MOUmeiqi/PhD-Resources/Misc. Images/2-r2.jpg

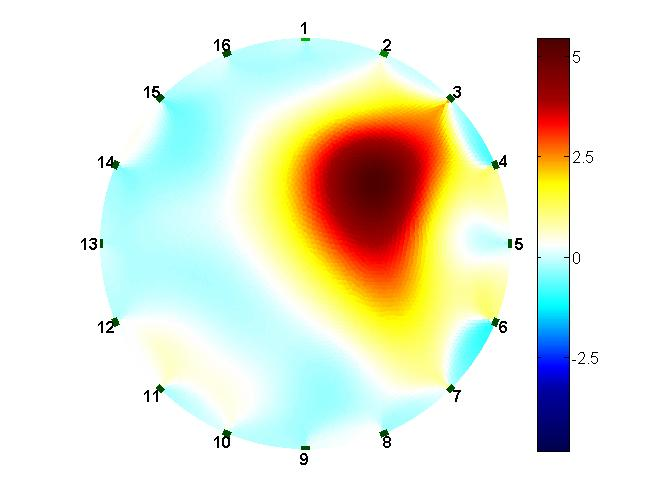
Misc. Images/2-r2.jpg
