MOUmeiqi/PhD-Resources/Misc. Images/3-r3a.jpg

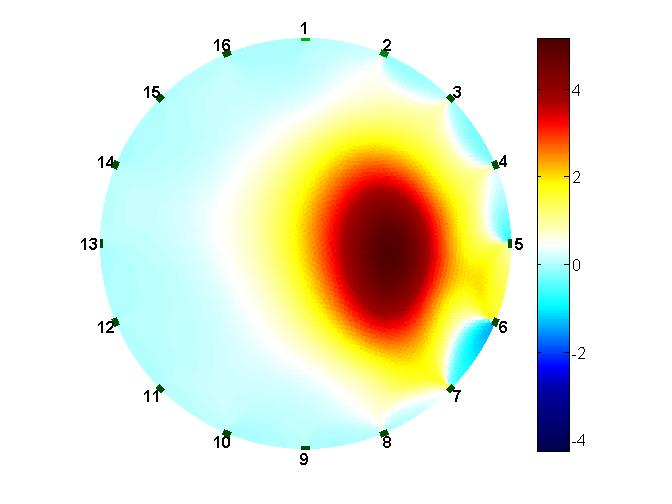
Misc. Images/3-r3a.jpg
