MOUmeiqi/PhD-Resources/Misc. Images/4-r4an.jpg

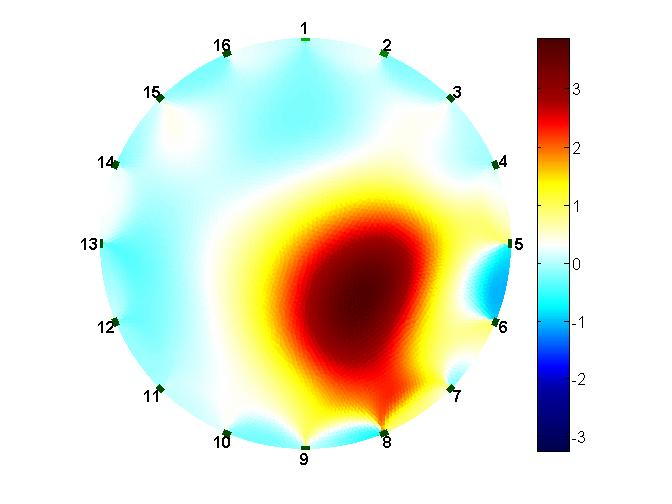
Misc. Images/4-r4an.jpg
