MOUmeiqi/PhD-Resources/Misc. Images/5-r5a.jpg

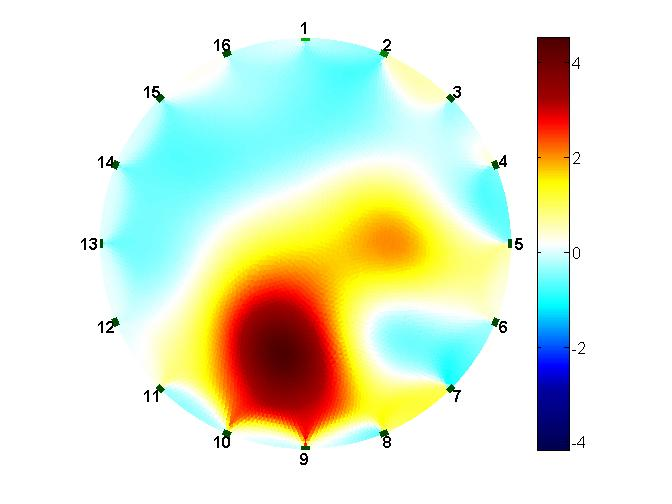
Misc. Images/5-r5a.jpg
