MOUmeiqi/PhD-Resources/Misc. Images/7-r7a.jpg

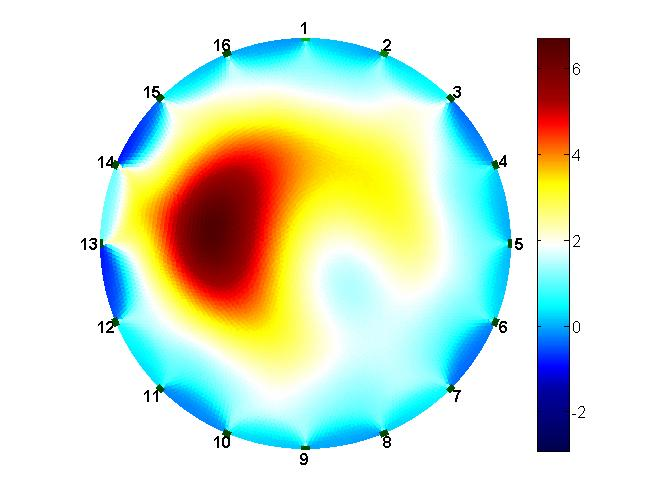
Misc. Images/7-r7a.jpg
