MOUmeiqi/PhD-Resources/Misc. Images/14-r103.jpg

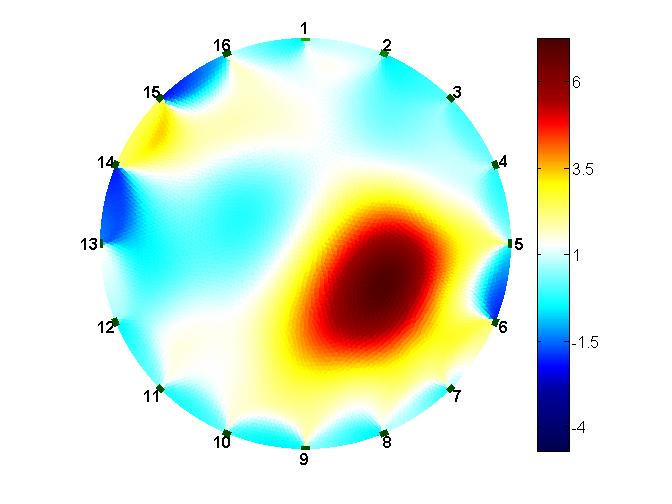
Misc. Images/14-r103.jpg
