MOUmeiqi/PhD-Resources/Misc. Images/n4aANDh4.jpg

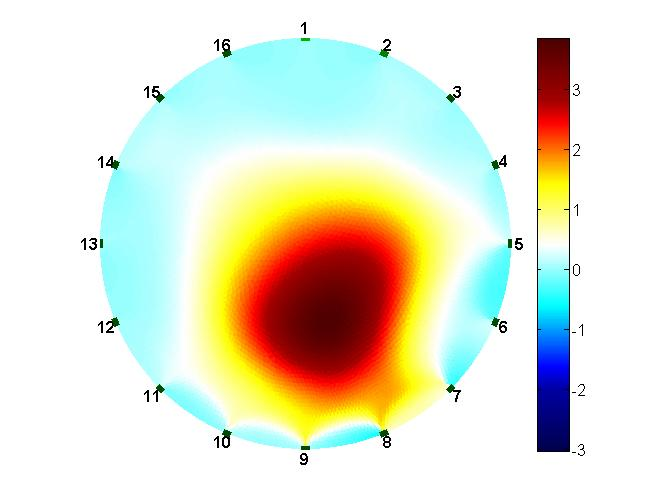
Misc. Images/n4aANDh4.jpg
