MOUmeiqi/PhD-Resources/Misc. Images/r1n.jpg

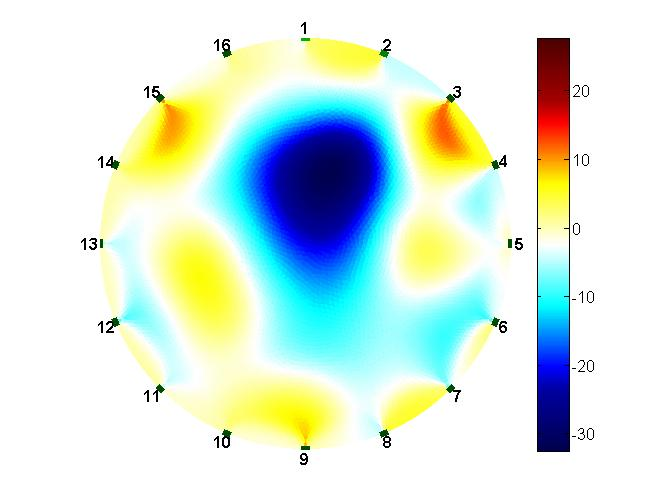
Misc. Images/r1n.jpg
