MOUmeiqi/PhD-Resources/Misc. Images/r2n.jpg

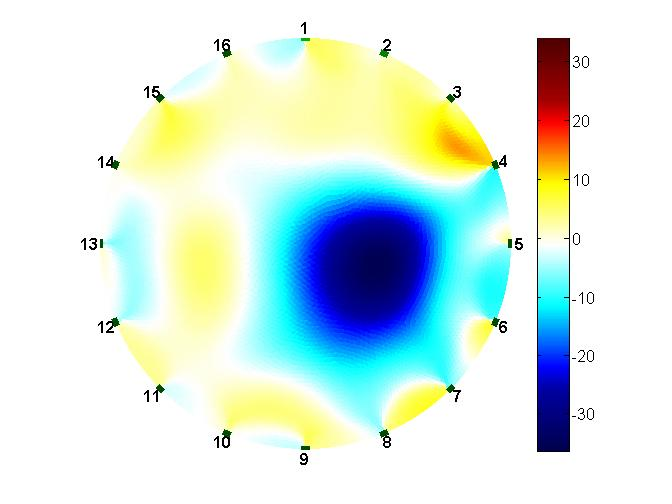
Misc. Images/r2n.jpg
