MOUmeiqi/PhD-Resources/Misc. Images/r3n.jpg

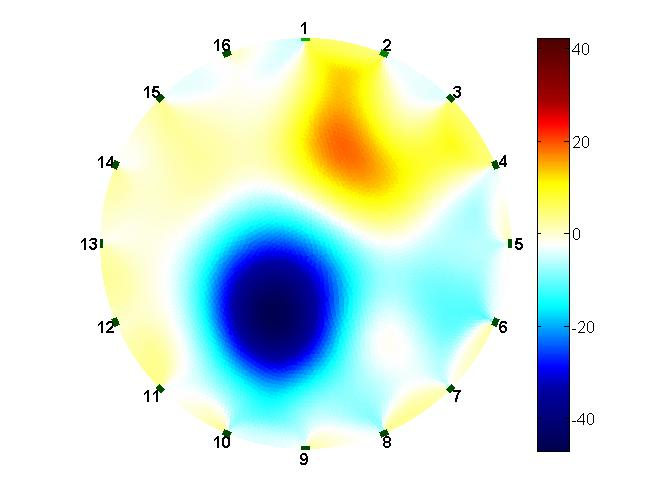
Misc. Images/r3n.jpg
