MOUmeiqi/PhD-Resources/Misc. Images/r6n.jpg

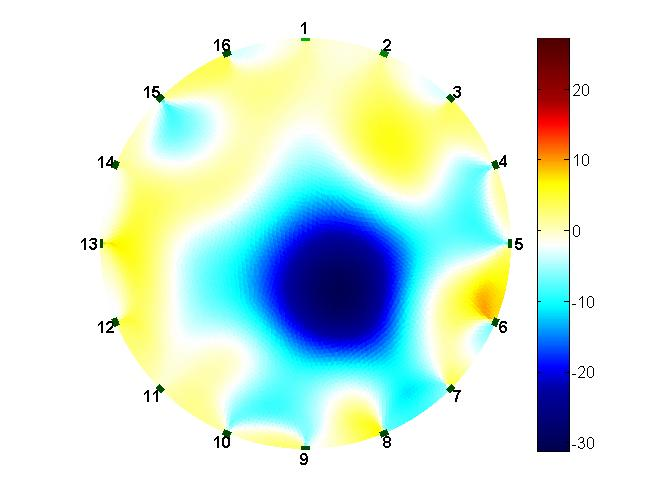
Misc. Images/r6n.jpg
