MOUmeiqi/PhD-Resources/Misc. Images/r7n.jpg

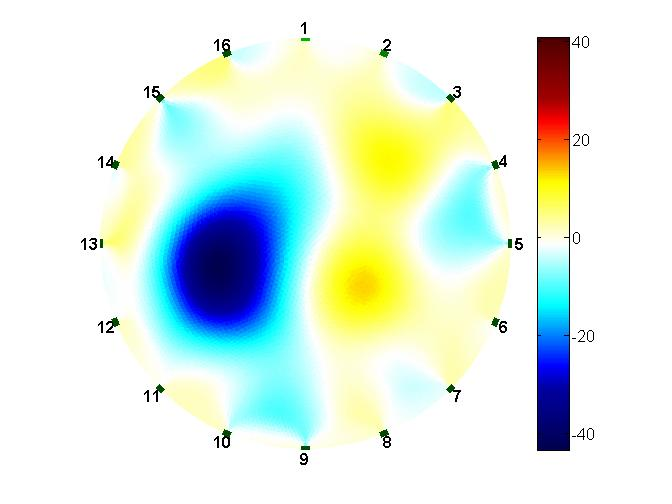
Misc. Images/r7n.jpg
