MOUmeiqi/PhD-Resources/Misc. Images/r8n.jpg

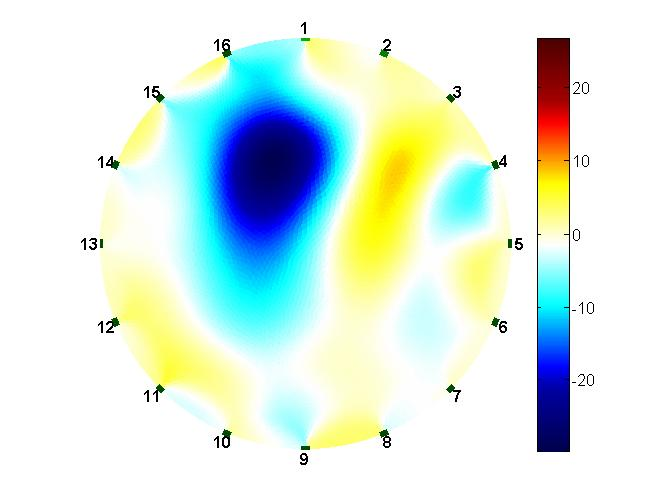
Misc. Images/r8n.jpg
