MOUmeiqi/PhD-Resources/Misc. Images/r11n.jpg

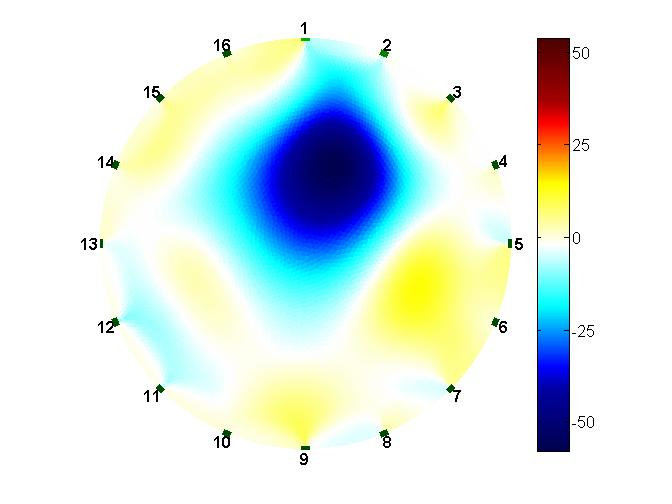
Misc. Images/r11n.jpg
