MOUmeiqi/PhD-Resources/Misc. Images/r21n.jpg

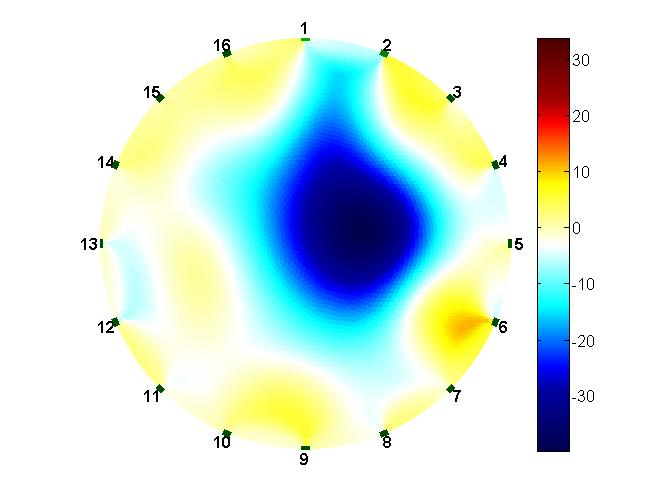
Misc. Images/r21n.jpg
