MOUmeiqi/PhD-Resources/Misc. Images/r31n.jpg

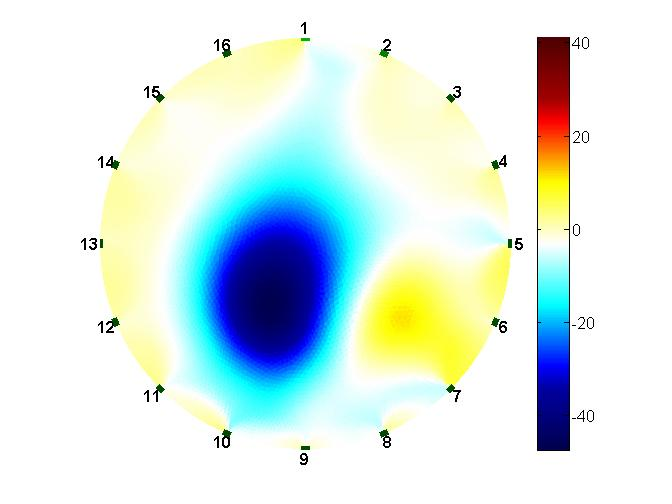
Misc. Images/r31n.jpg
