MOUmeiqi/PhD-Resources/Misc. Images/r41n.jpg

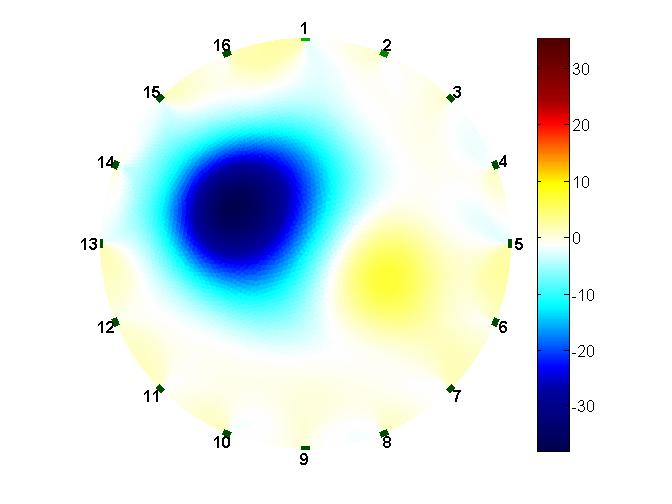
Misc. Images/r41n.jpg
