MOUmeiqi/PhD-Resources/Misc. Images/r_n2a_h2a.jpg

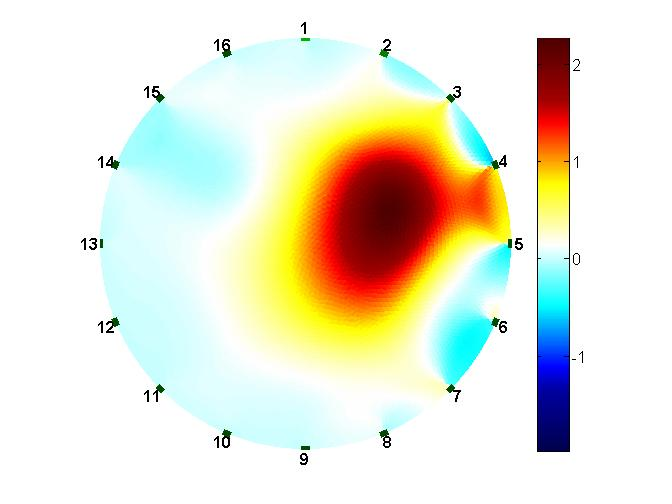
Misc. Images/r_n2a_h2a.jpg
