MOUmeiqi/PhD-Resources/Misc. Images/r_n3a_h3a.jpg

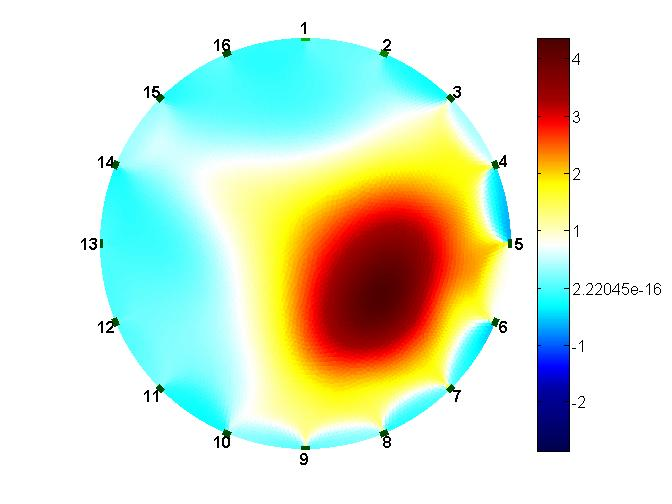
Misc. Images/r_n3a_h3a.jpg
