MOUmeiqi/PhD-Resources/Misc. Images/r_n3a_h3a_2.jpg

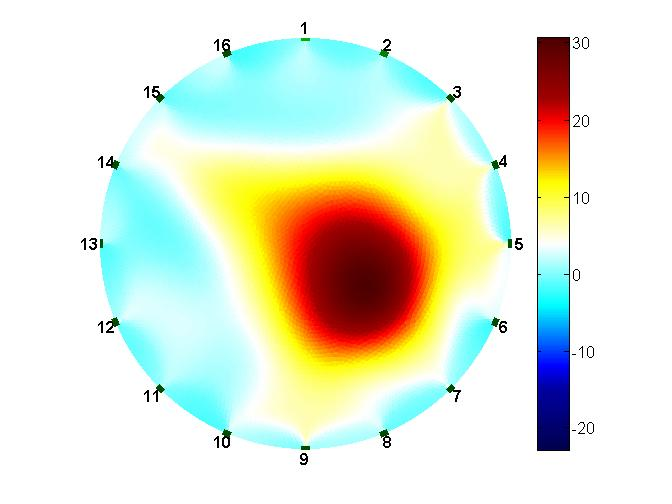
Misc. Images/r_n3a_h3a_2.jpg
