MOUmeiqi/PhD-Resources/Misc. Images/r_n4a_h4.jpg

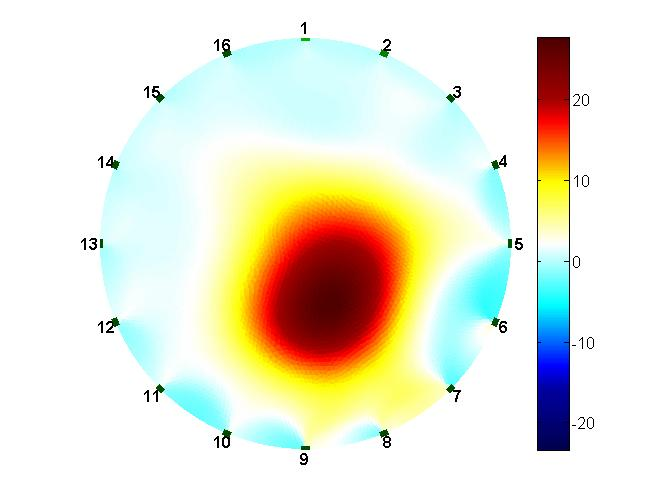
Misc. Images/r_n4a_h4.jpg
