MOUmeiqi/PhD-Resources/Misc. Images/r_n5a_h5_2.jpg

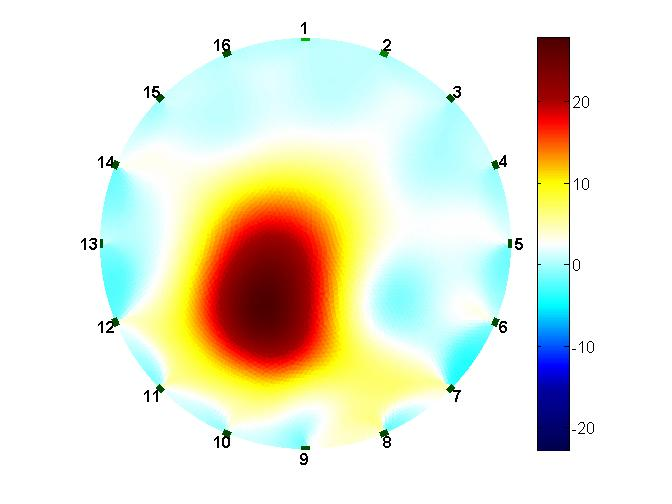
Misc. Images/r_n5a_h5_2.jpg
