MOUmeiqi/PhD-Resources/Misc. Images/r_n6a_h6.jpg

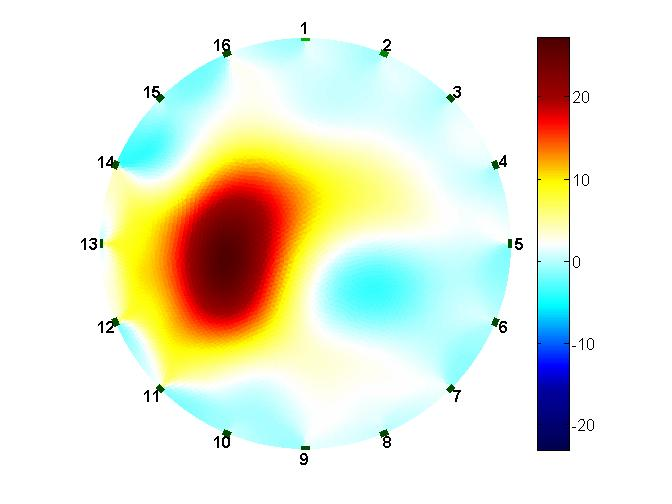
Misc. Images/r_n6a_h6.jpg
