MOUmeiqi/PhD-Resources/Misc. Images/r_n7a_h7.jpg

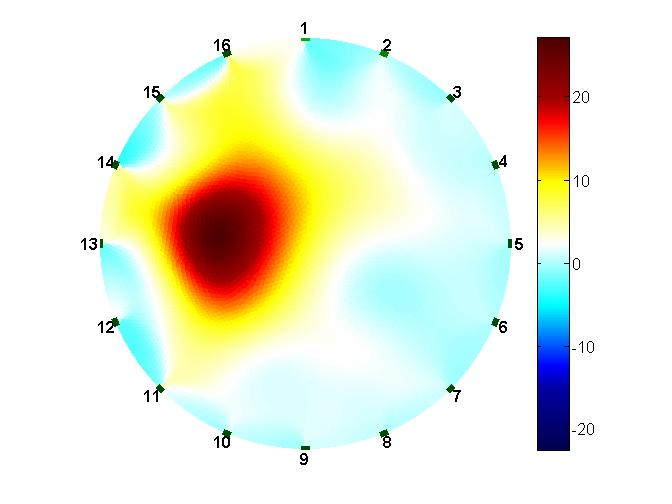
Misc. Images/r_n7a_h7.jpg
