MOUmeiqi/PhD-Resources/Misc. Images/rd1.jpg

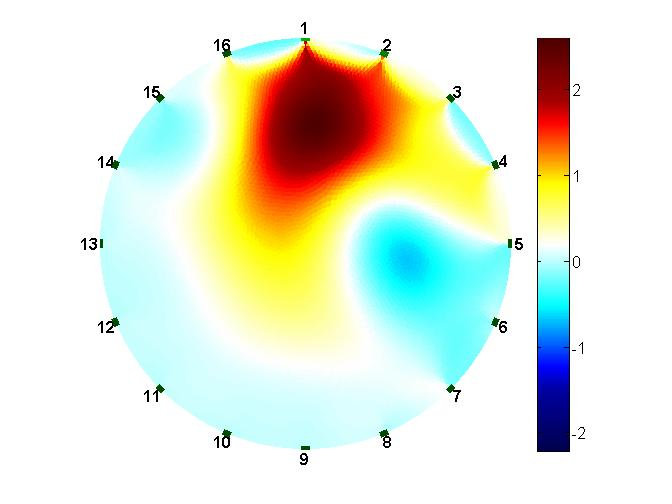
Misc. Images/rd1.jpg
