MOUmeiqi/PhD-Resources/Misc. Images/rd2.jpg

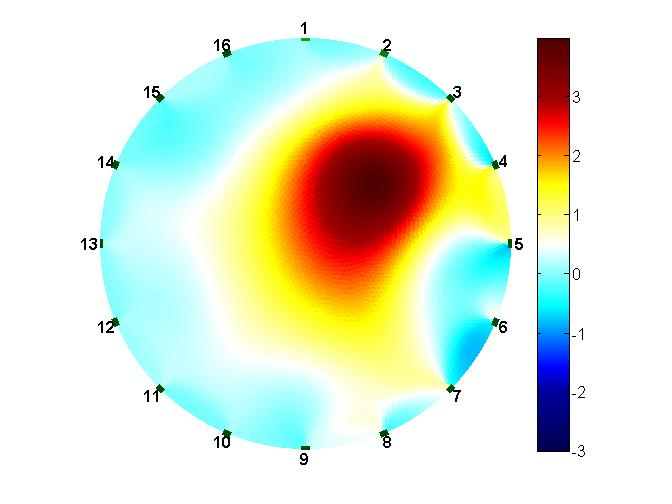
Misc. Images/rd2.jpg
