MOUmeiqi/PhD-Resources/Misc. Images/rd3.jpg

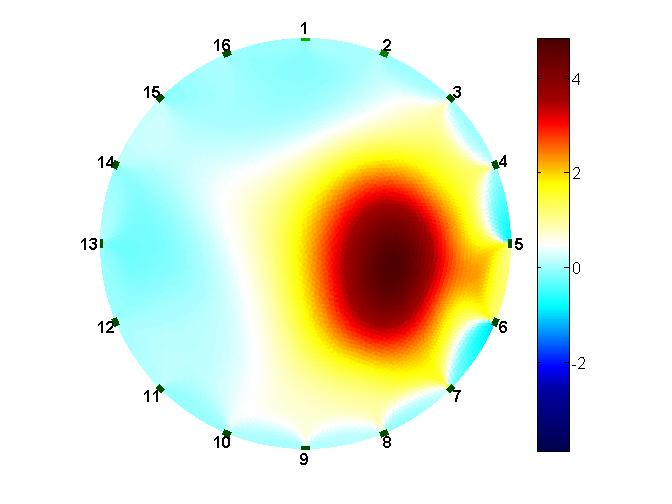
Misc. Images/rd3.jpg
