MOUmeiqi/PhD-Resources/Misc. Images/rd4.jpg

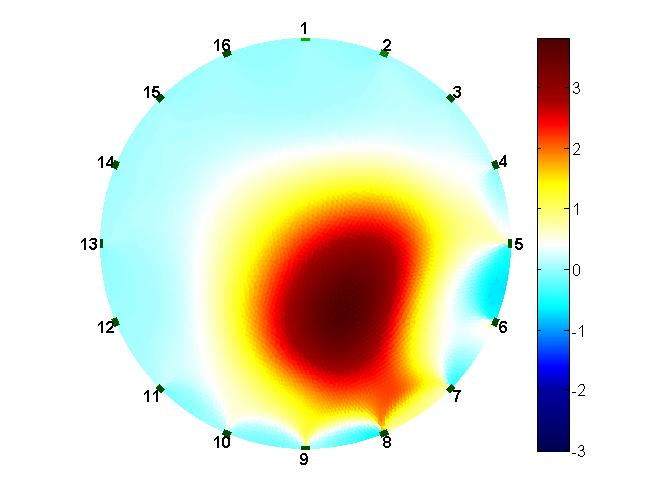
Misc. Images/rd4.jpg
