MOUmeiqi/PhD-Resources/Misc. Images/rd4n.jpg

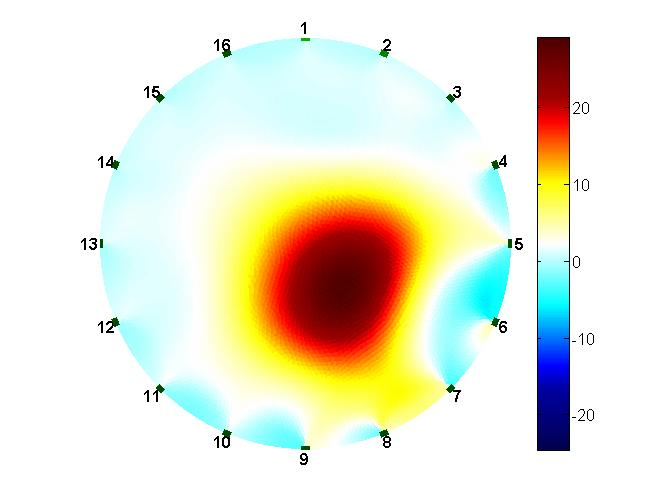
Misc. Images/rd4n.jpg
