MOUmeiqi/PhD-Resources/Misc. Images/rd5.jpg

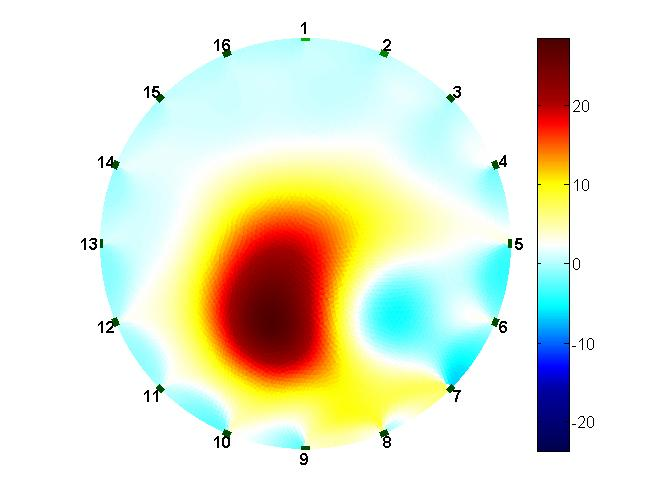
Misc. Images/rd5.jpg
