MOUmeiqi/PhD-Resources/Misc. Images/rd9.jpg

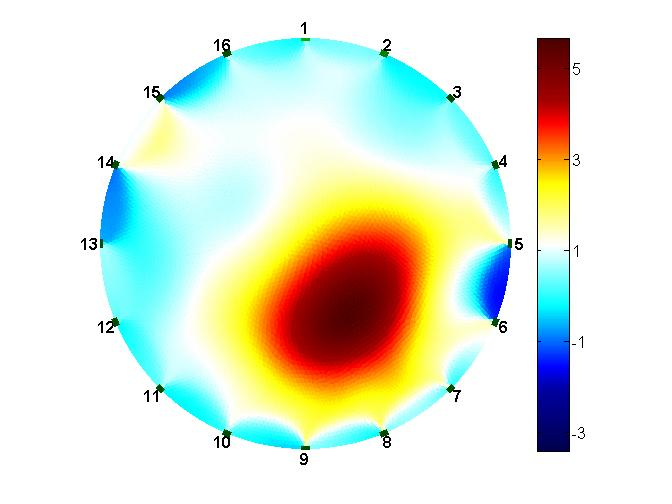
Misc. Images/rd9.jpg
