MOUmeiqi/PhD-Resources/Misc. Images/rdf1n.jpg

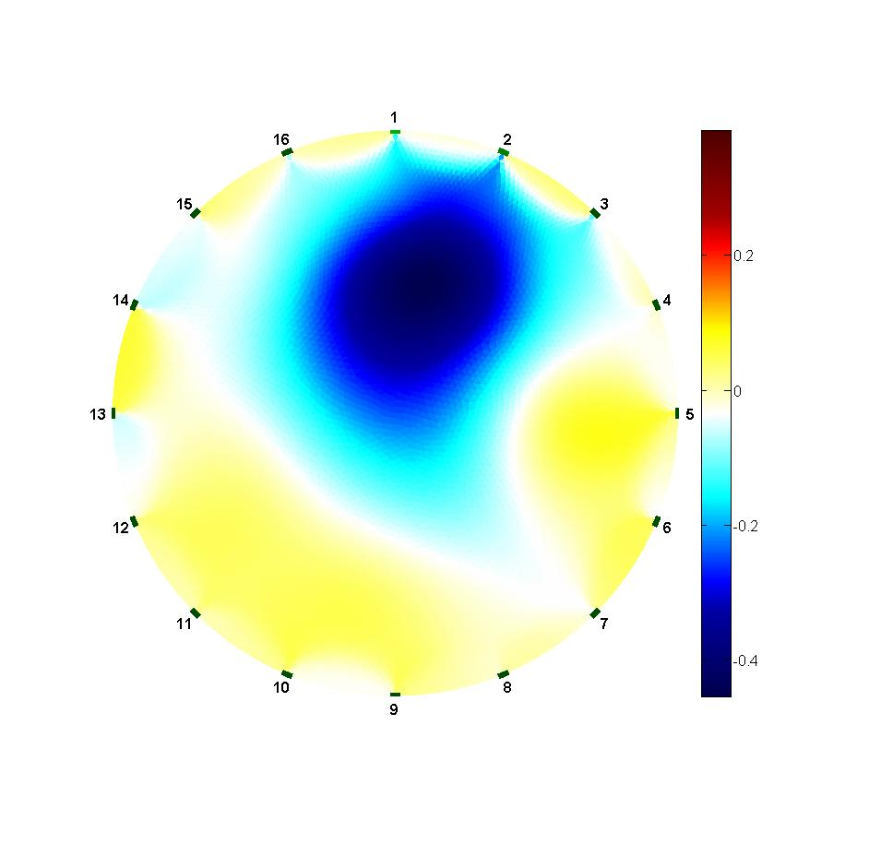
Misc. Images/rdf1n.jpg
