MOUmeiqi/PhD-Resources/Misc. Images/rdf2.jpg

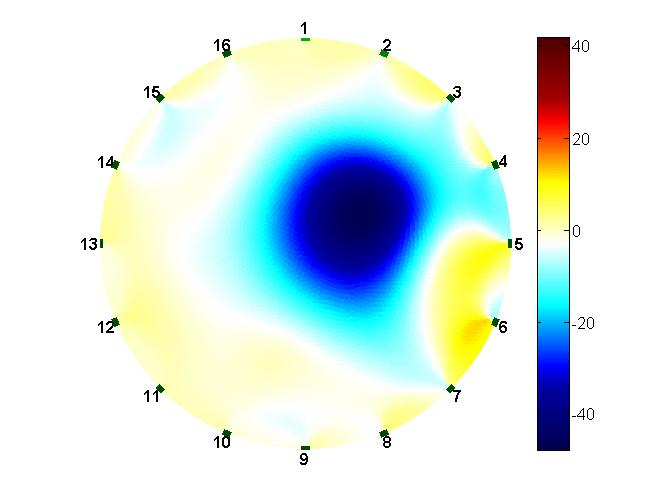
Misc. Images/rdf2.jpg
