MOUmeiqi/PhD-Resources/Misc. Images/rdf3.jpg

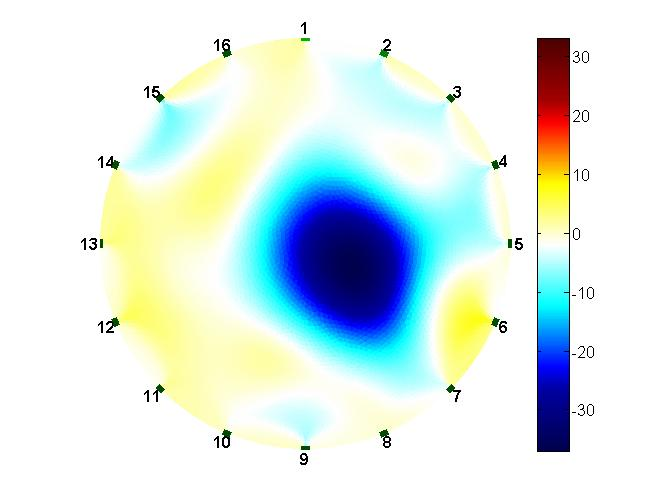
Misc. Images/rdf3.jpg
