MOUmeiqi/PhD-Resources/Misc. Images/rdf4.jpg

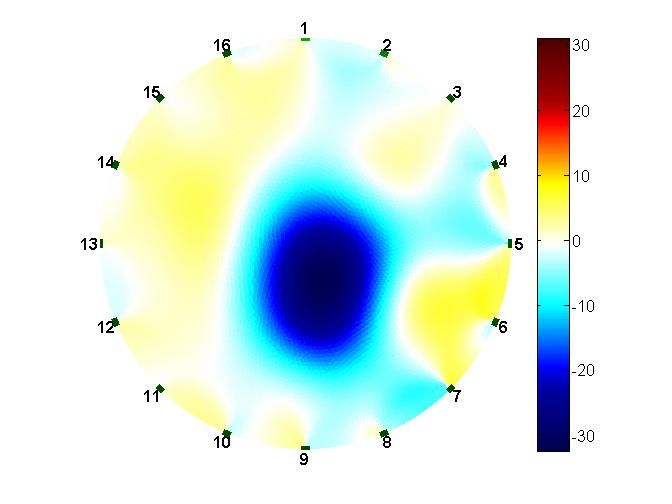
Misc. Images/rdf4.jpg
