MOUmeiqi/PhD-Resources/Misc. Images/rdf5.jpg

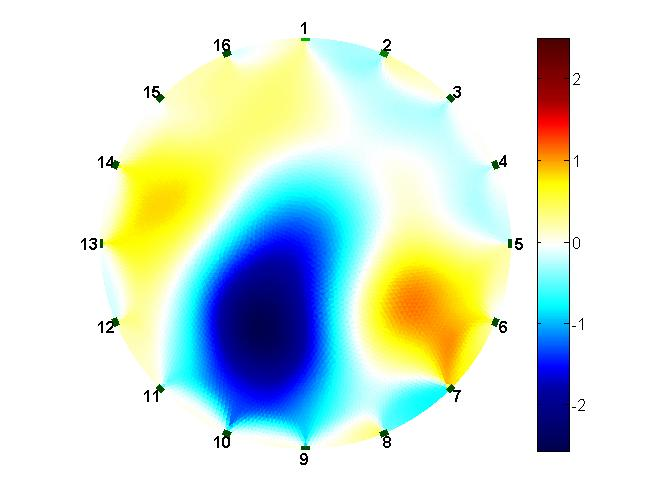
Misc. Images/rdf5.jpg
