MOUmeiqi/PhD-Resources/Misc. Images/rdf5n.jpg

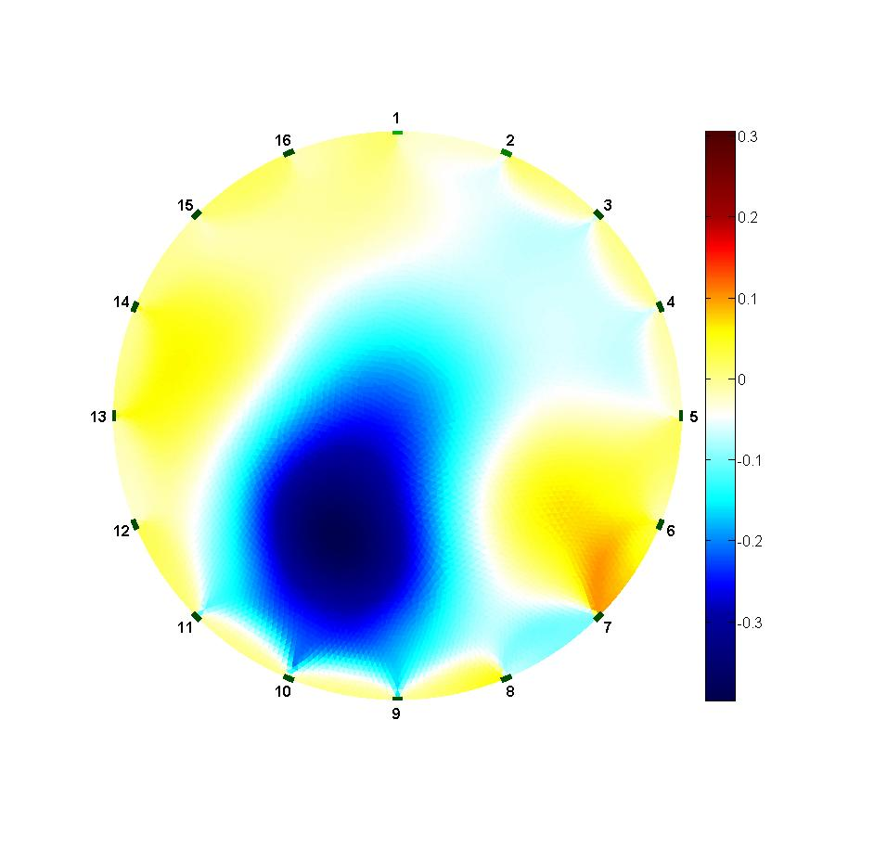
Misc. Images/rdf5n.jpg
