MOUmeiqi/PhD-Resources/Misc. Images/rdf6.jpg

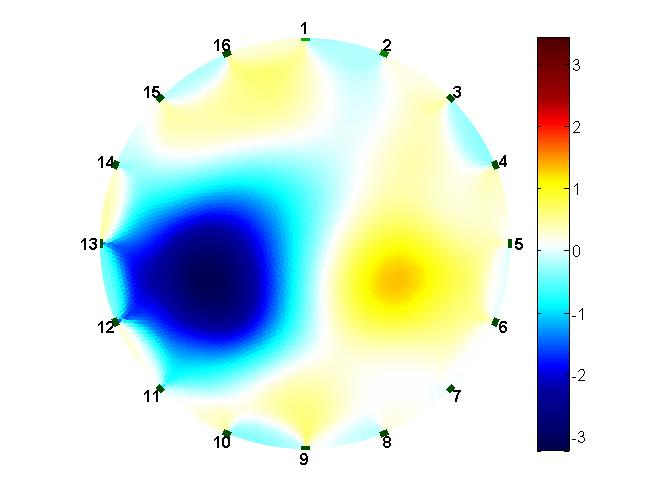
Misc. Images/rdf6.jpg
