MOUmeiqi/PhD-Resources/Misc. Images/rdf7.jpg

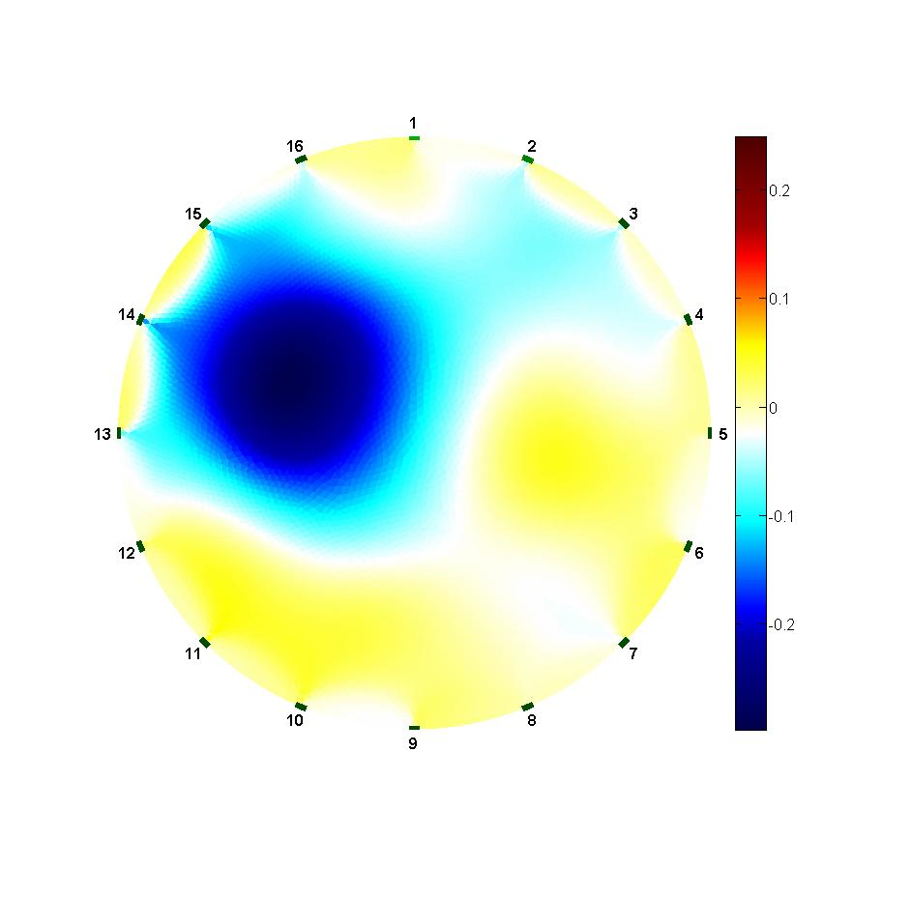
Misc. Images/rdf7.jpg
