MOUmeiqi/PhD-Resources/Misc. Images/rdf8.jpg

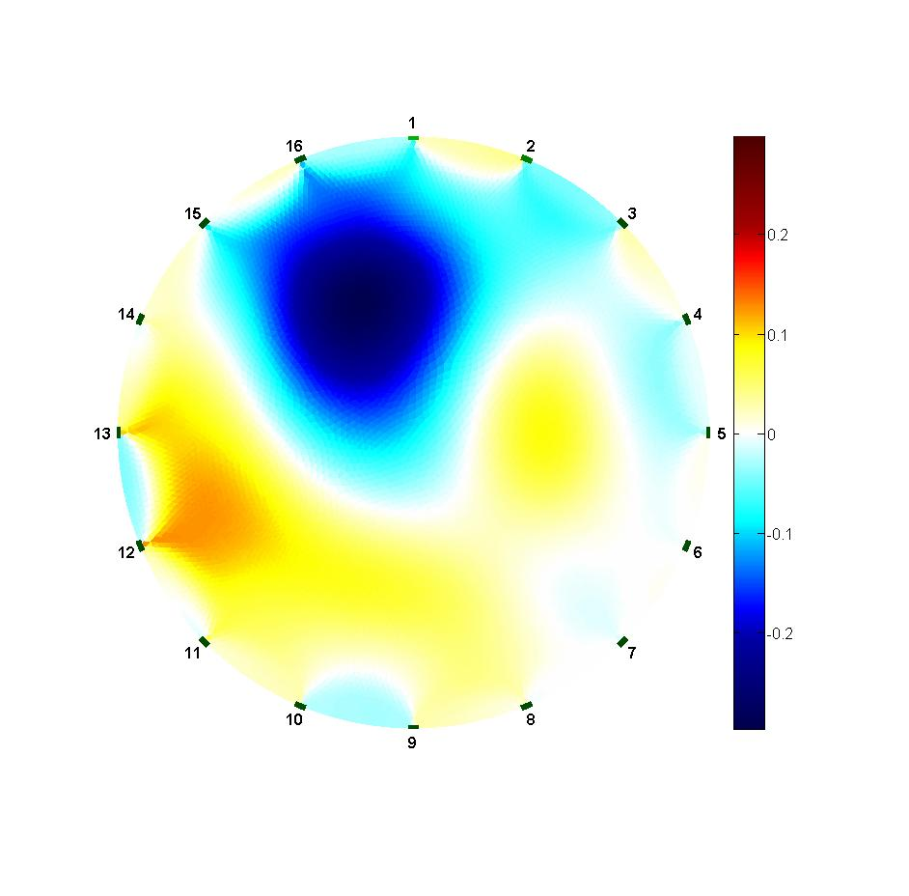
Misc. Images/rdf8.jpg
