MOUmeiqi/PhD-Resources/Misc. Images/rdf9.jpg

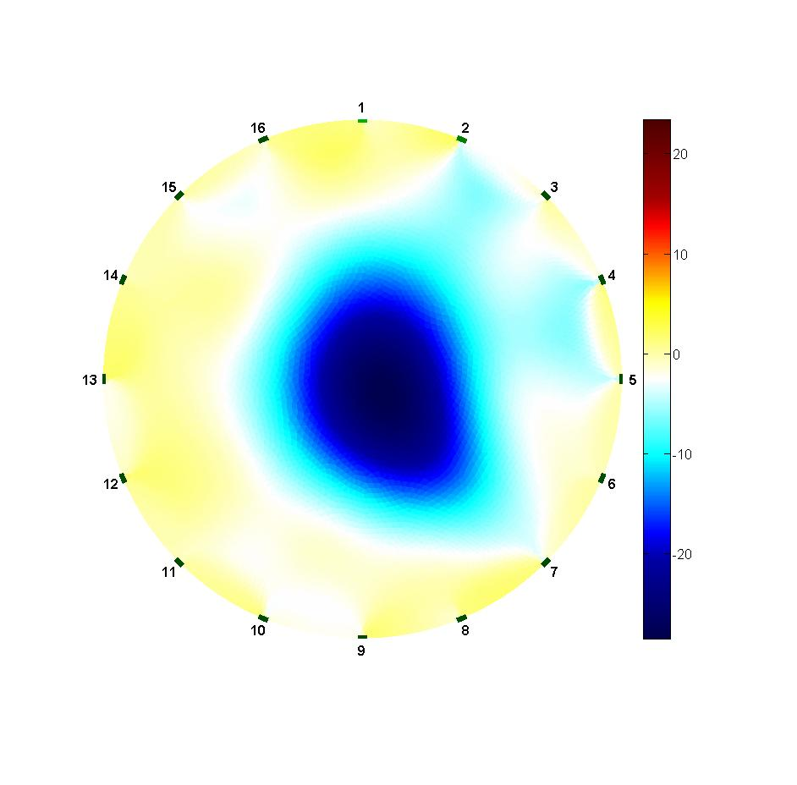
Misc. Images/rdf9.jpg
