MOUmeiqi/PhD-Resources/Misc. Images/rDOUBLE2.jpg

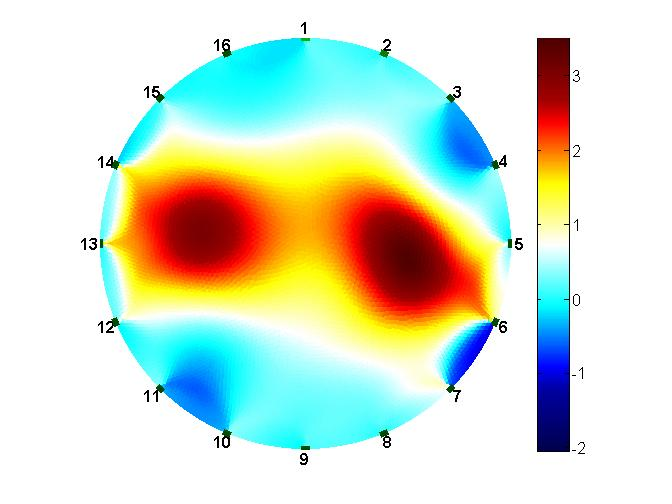
Misc. Images/rDOUBLE2.jpg
