MOUmeiqi/PhD-Resources/Misc. Images/rDOUBLE4.jpg

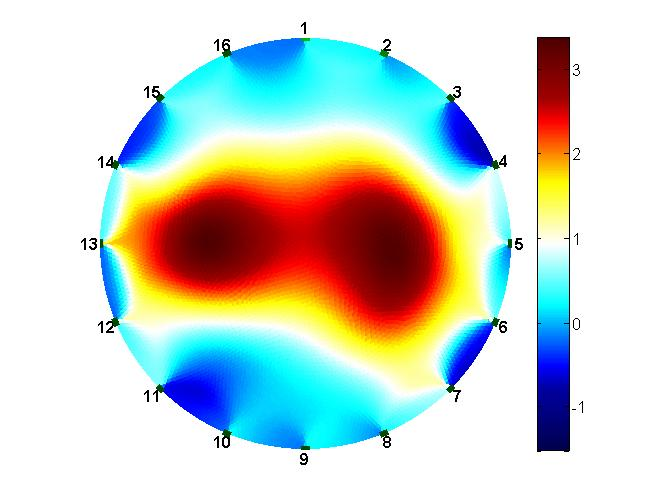
Misc. Images/rDOUBLE4.jpg
