MOUmeiqi/PhD-Resources/Misc. Images/rDOUBLE.jpg

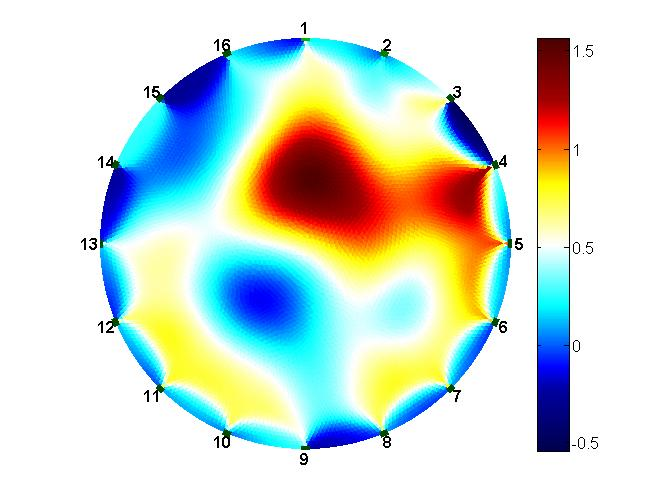
Misc. Images/rDOUBLE.jpg
