MOUmeiqi/PhD-Resources/Misc. Images/repeatability/r1/r11.jpg

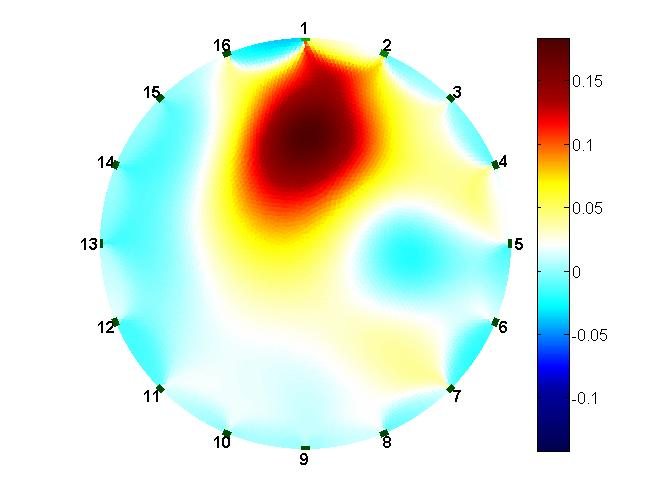
Misc. Images/repeatability/r1/r11.jpg
