MOUmeiqi/PhD-Resources/Misc. Images/repeatability/r1/r12.jpg

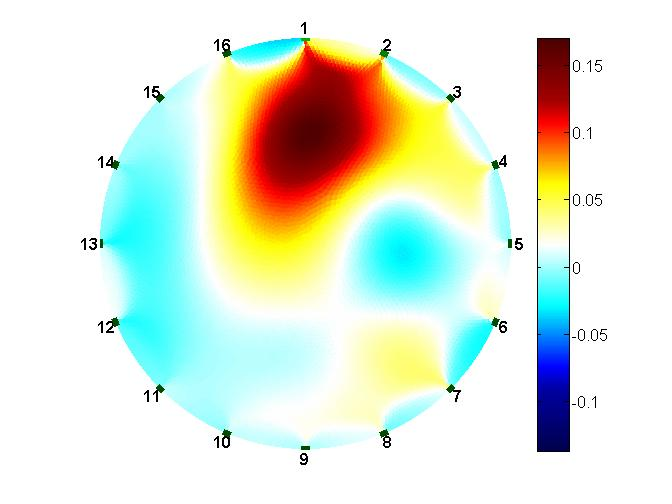
Misc. Images/repeatability/r1/r12.jpg
