MOUmeiqi/PhD-Resources/Misc. Images/repeatability/r1/r14.jpg

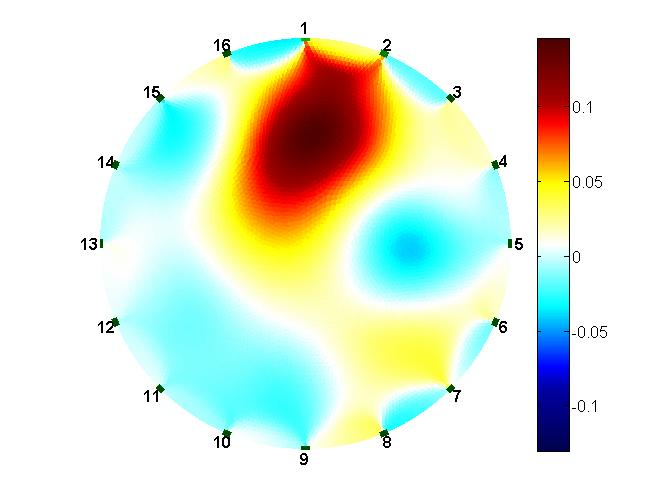
Misc. Images/repeatability/r1/r14.jpg
