MOUmeiqi/PhD-Resources/Misc. Images/repeatability/r2/r21.jpg

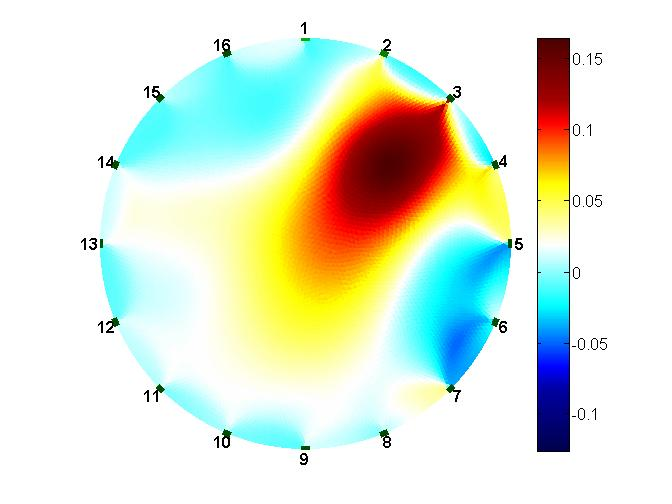
Misc. Images/repeatability/r2/r21.jpg
