MOUmeiqi/PhD-Resources/Misc. Images/repeatability/r3/r32.jpg

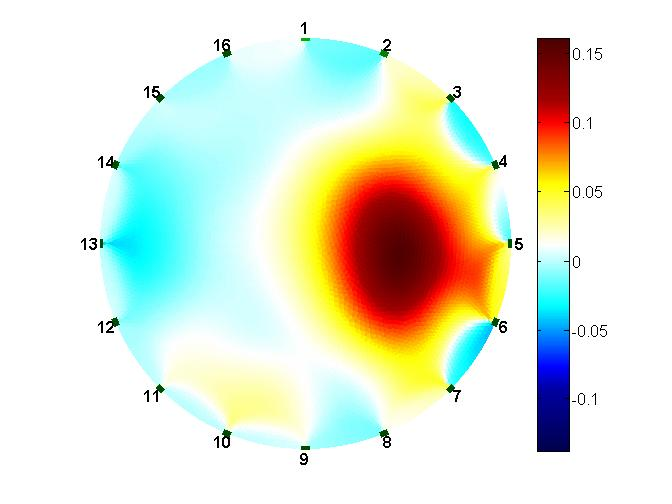
Misc. Images/repeatability/r3/r32.jpg
