MOUmeiqi/PhD-Resources/Misc. Images/repeatability/r3/r33.jpg

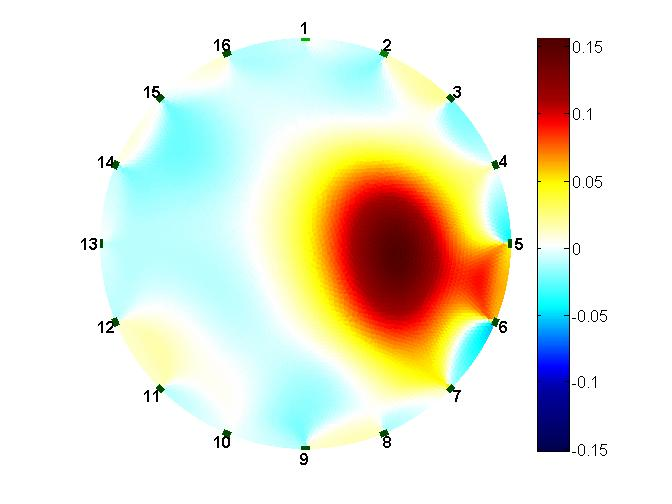
Misc. Images/repeatability/r3/r33.jpg
