MOUmeiqi/PhD-Resources/Misc. Images/repeatability/r4/r41.jpg

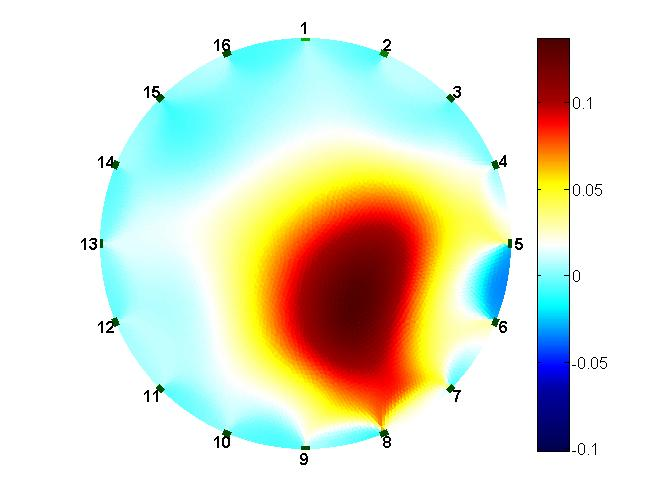
Misc. Images/repeatability/r4/r41.jpg
