MOUmeiqi/PhD-Resources/Misc. Images/repeatability/r4/r44.jpg

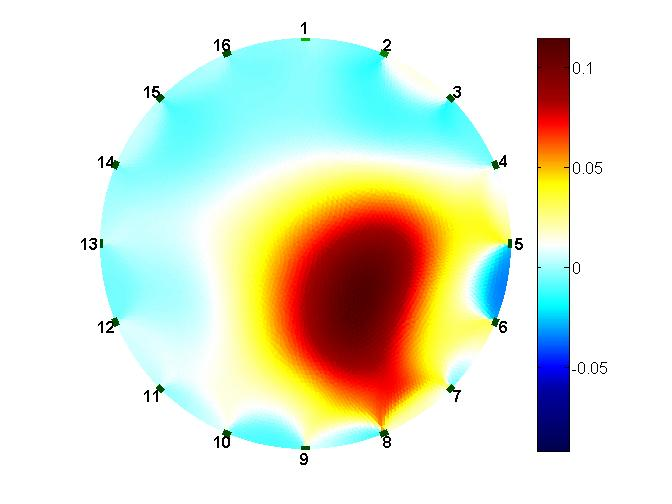
Misc. Images/repeatability/r4/r44.jpg
