MOUmeiqi/PhD-Resources/Misc. Images/repeatability/r4/r45.jpg

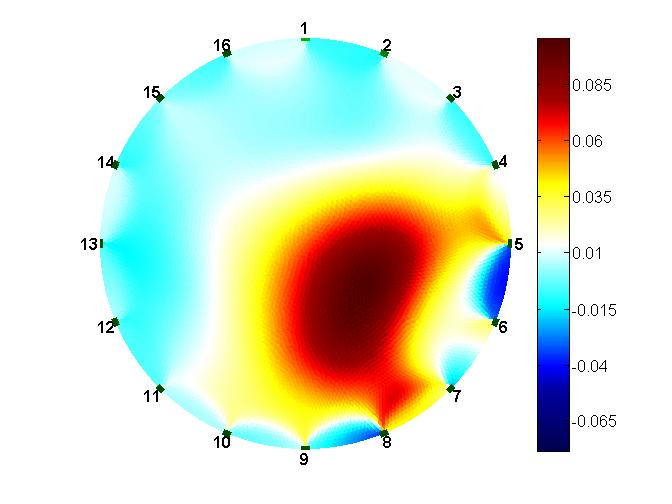
Misc. Images/repeatability/r4/r45.jpg
