MOUmeiqi/PhD-Resources/Misc. Images/repeatability/r5/r51.jpg

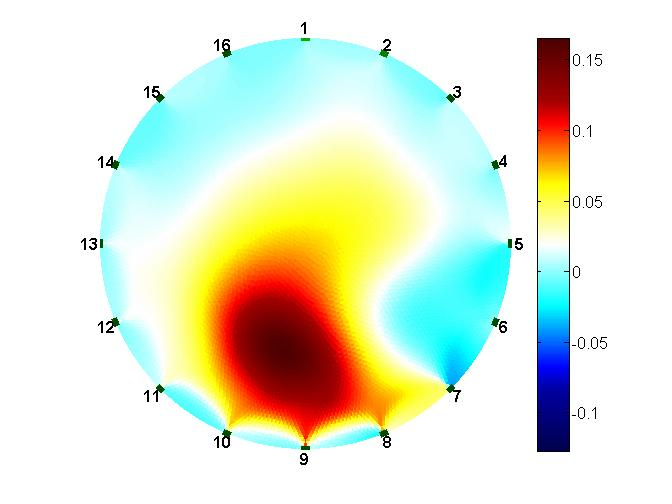
Misc. Images/repeatability/r5/r51.jpg
