MOUmeiqi/PhD-Resources/Misc. Images/repeatability/r5/r53.jpg

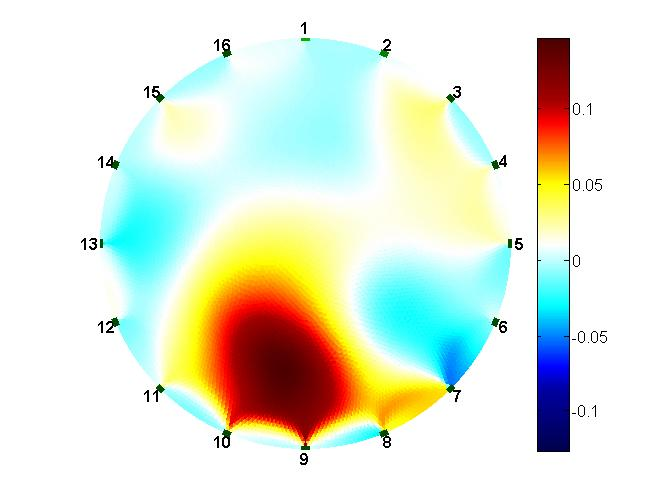
Misc. Images/repeatability/r5/r53.jpg
