MOUmeiqi/PhD-Resources/Misc. Images/repeatability/r5/r54.jpg

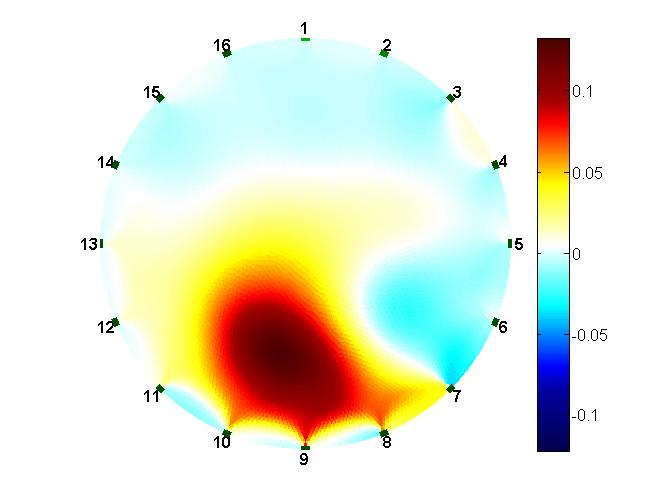
Misc. Images/repeatability/r5/r54.jpg
