MOUmeiqi/PhD-Resources/Misc. Images/repeatability/r5/r55.jpg

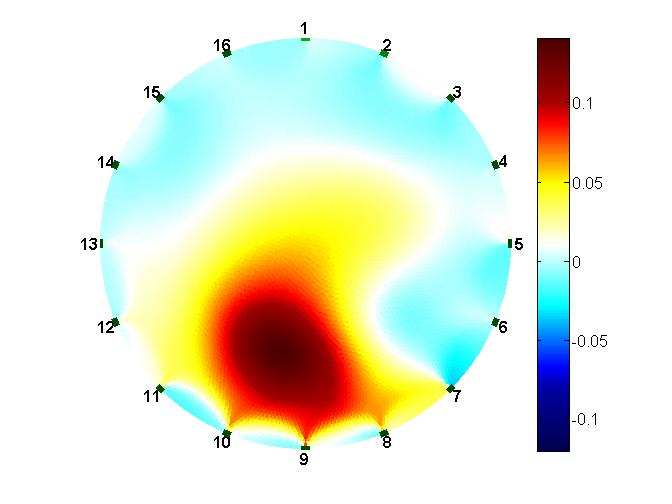
Misc. Images/repeatability/r5/r55.jpg
