MOUmeiqi/PhD-Resources/Misc. Images/repeatability/r6/r61.jpg

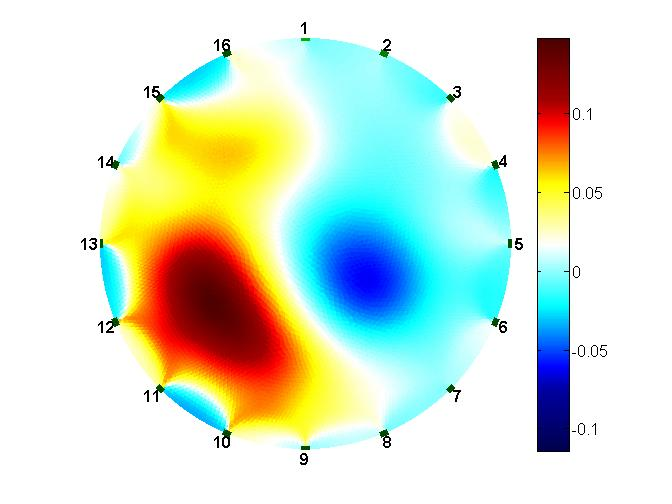
Misc. Images/repeatability/r6/r61.jpg
