MOUmeiqi/PhD-Resources/Misc. Images/repeatability/r6/r63.jpg

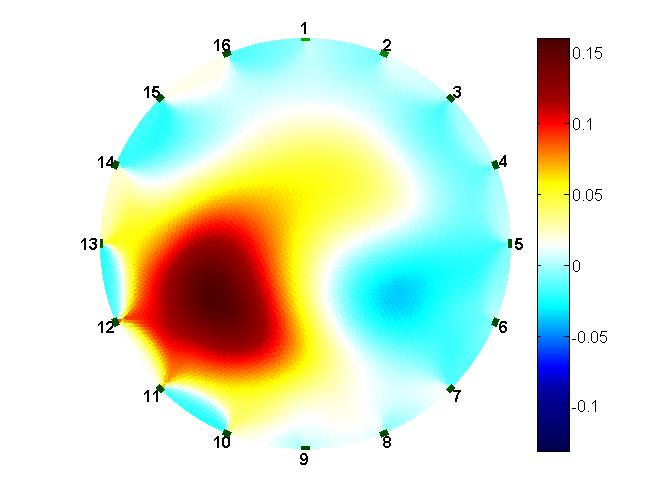
Misc. Images/repeatability/r6/r63.jpg
