MOUmeiqi/PhD-Resources/Misc. Images/repeatability/r6/r64.jpg

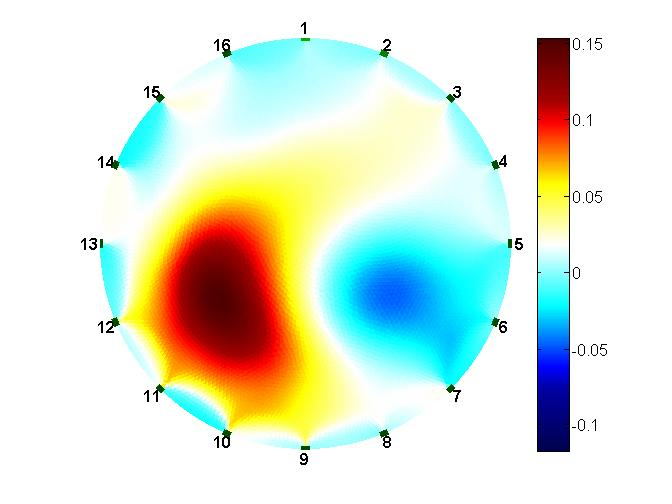
Misc. Images/repeatability/r6/r64.jpg
