MOUmeiqi/PhD-Resources/Misc. Images/repeatability/r6/r65.jpg

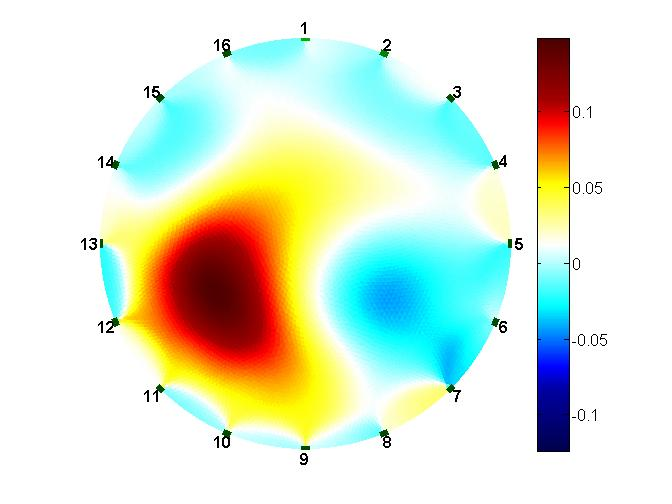
Misc. Images/repeatability/r6/r65.jpg
