MOUmeiqi/PhD-Resources/Misc. Images/repeatability/r7/r71.jpg

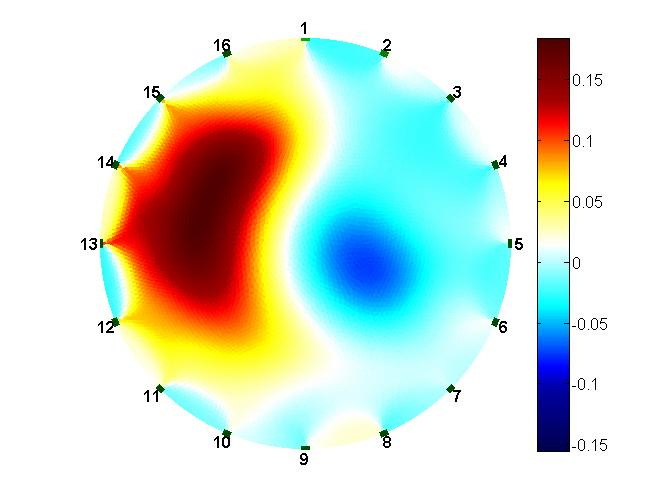
Misc. Images/repeatability/r7/r71.jpg
