MOUmeiqi/PhD-Resources/Misc. Images/repeatability/r7/r74.jpg

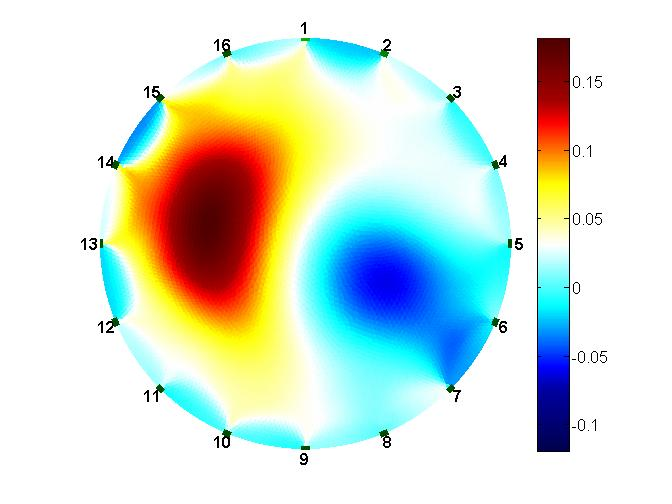
Misc. Images/repeatability/r7/r74.jpg
