MOUmeiqi/PhD-Resources/Misc. Images/repeatability/r8/r81.jpg

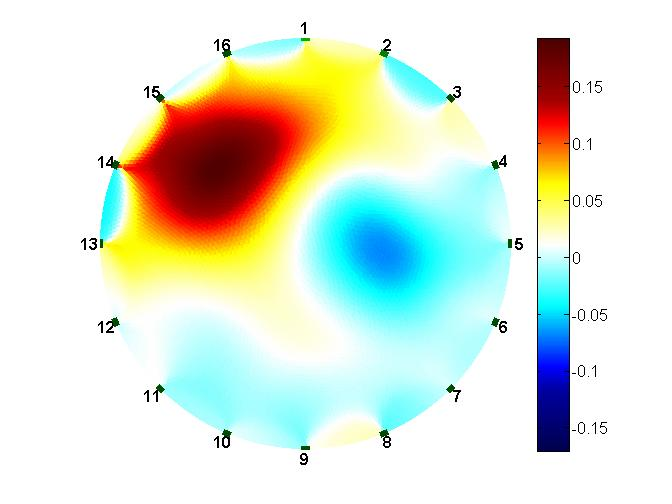
Misc. Images/repeatability/r8/r81.jpg
