MOUmeiqi/PhD-Resources/Misc. Images/repeatability/r8/r83.jpg

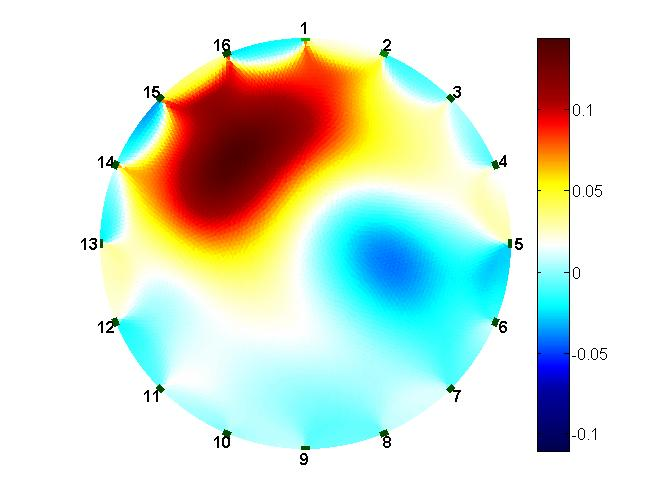
Misc. Images/repeatability/r8/r83.jpg
