MOUmeiqi/PhD-Resources/Misc. Images/repeatability/r8/r85.jpg

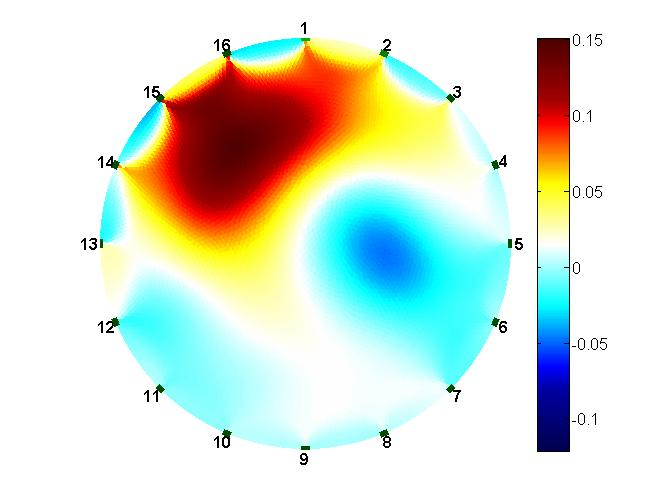
Misc. Images/repeatability/r8/r85.jpg
