MOUmeiqi/PhD-Resources/Schematics/Working LTSpice simulations/instrument voltage difference amplifier.asc

R1: res; 1k
R2: res; 1k
R3: res; 1k
R4: res; 1k
R5: res; 1k
R6: res; 1k
R7: res; 1k
U1: AD795
U2: AD795
U3: AD795
V1: voltage; 2
V2: voltage; 1
V3: voltage; 12
V4: voltage; -12
Named nets: 0
.tran 0 1 0 0.01
