MOUmeiqi/PhD-Resources/VHDL_CODE/V/FIR_3MHz_low_silent_param.txt

fc_version : 11.0
blank_gen : READ
coef_bit_width : 17
coef_conv_sel : AUTO
coef_pow2 : FALSE
data_type : USN
in_bit_width : 14
num_ch : 1
out_calc_basis : 0
fir_bit_width : 36
out_full_chk : 0
out_sbf_chk : 0
out_msb_rad : MSB_SAT
out_lsb_rad : LSB_TRN
out_lose_msb : 0
out_lose_lsb : 22
arch_struct_sel : 3
arch_data_store : 0
arch_coef_store : 0
arch_reload_coef : 0
arch_reload_coef_sgl_clock : 0
arch_num_mbs : 2
arch_no_sym : 0
num_bank_set : 1
length : 37
num_cycles : 1
arch_pipeline : 1
poly_type : 0
poly_fact : 2
device_family : 30
use_dsp_block : 0
rate_ctrl : RATE_CTRL_OFF
arch_no_ctrl : 0
m_file_gen : 1
vec_file_gen : 1
vec_clk_per : 10.0
is_reg_test : 0
netlist_only : 0
hardcopy_selected : 0
