MOUmeiqi/PhD-Resources/VHDL_CODE/V/FIR_3MHZ_low_sim/FIR_3MHZ_low_param.txt

PhysChanIn : 1 
PhysChanOut : 1 
ChansPerPhyIn : 1 
ChansPerPhyOut : 1 
InWidth : 14 
InFracWidth : 0 
OutWidth : 14 
OutFullWidth : 37 
OutFracWidth : 0 
OutFullFracWidth : 0 
nChans : 1 
nTaps : 37 
clockRate : 100 
inRate : 100 
interpN : 1 
decimN : 1 
busDataWidth : 32 
bankInWidth : 0 
